bschan9228/MInG/Website/images/FP_slide.png

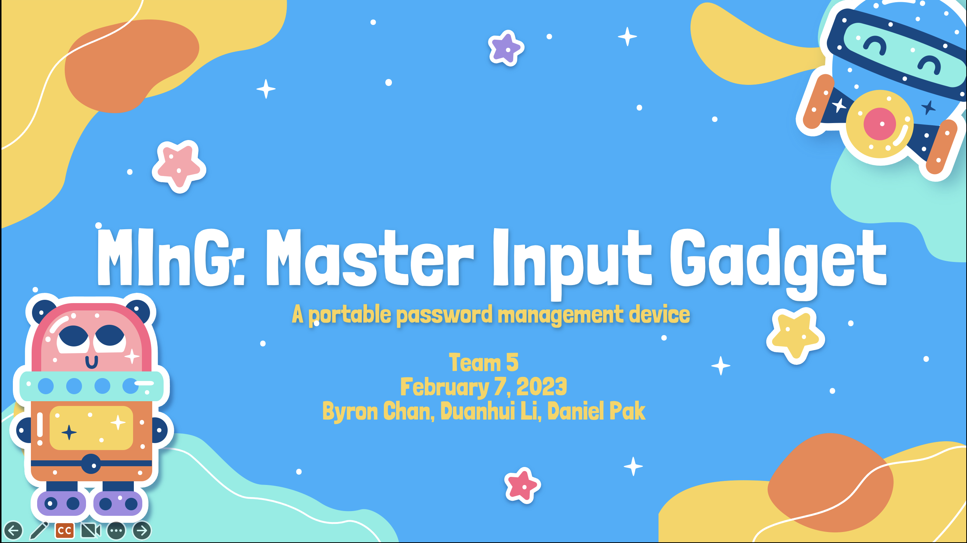
Website/images/FP_slide.png
