bschan9228/MInG/Website/images/IMG_0258.jpg

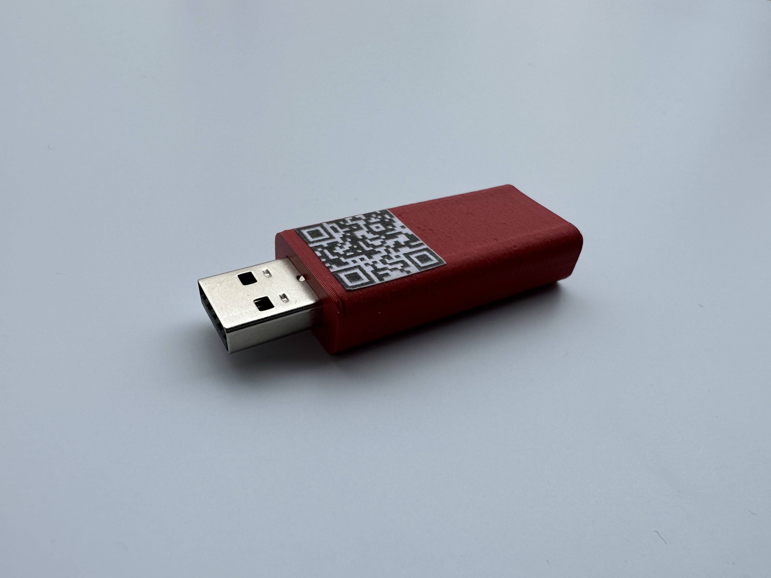
Website/images/IMG_0258.jpg
