bschan9228/MInG/Website/images/IMG_0273.jpg

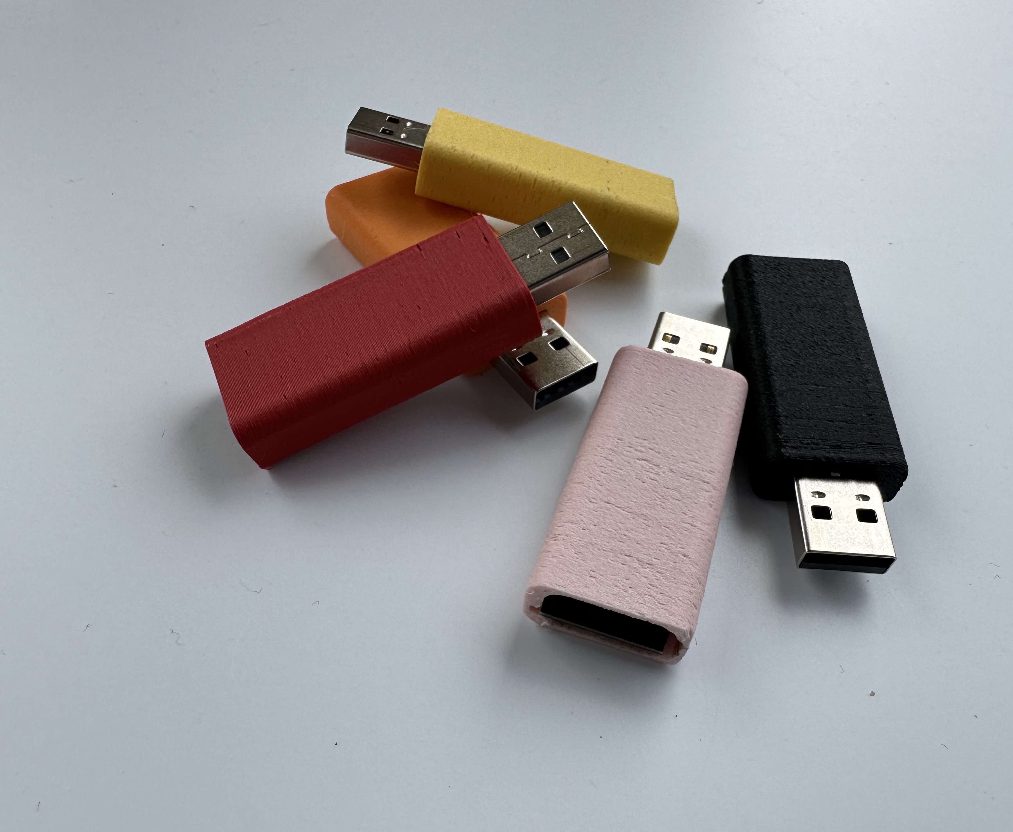
Website/images/IMG_0273.jpg
