bschan9228/MInG/Website/images/IMG_0285.jpg

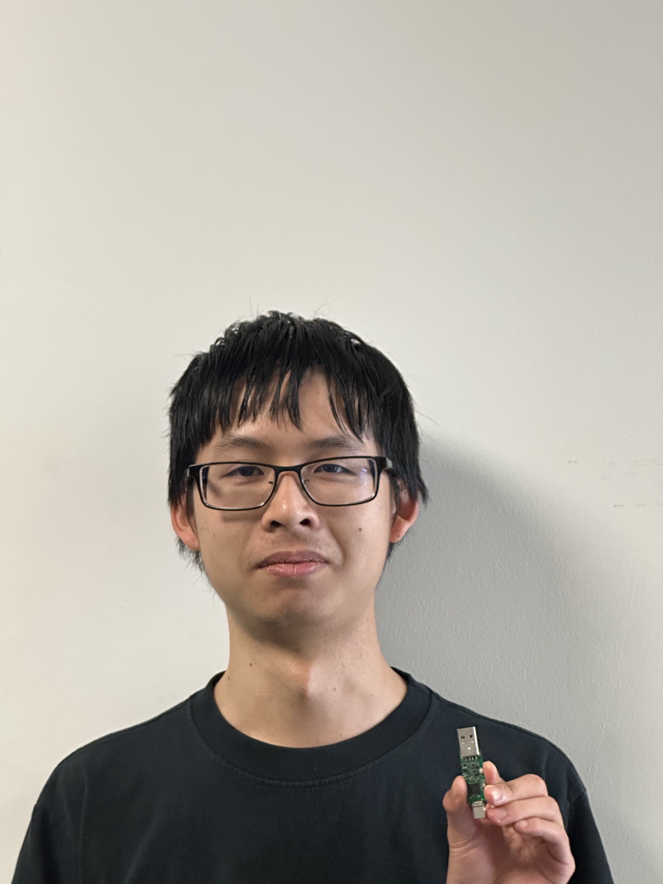
Website/images/IMG_0285.jpg
