bschan9228/MInG/Website/images/IMG_0287.jpg

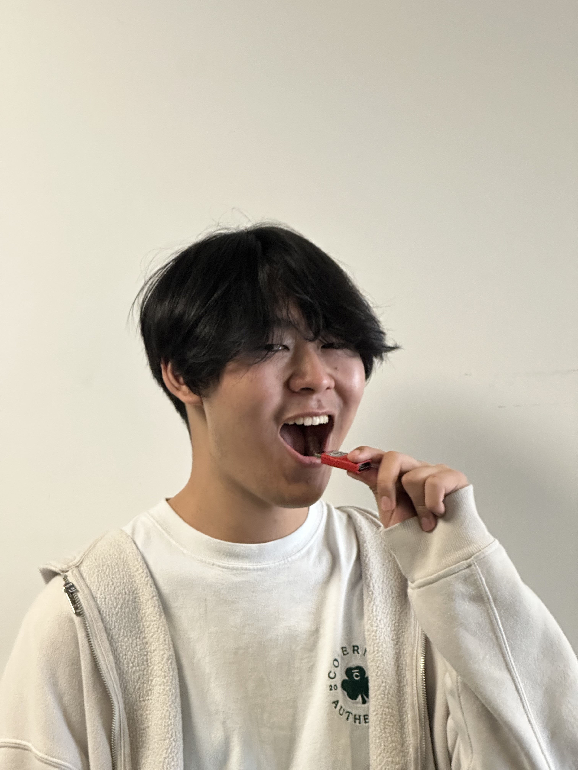
Website/images/IMG_0287.jpg
