bschan9228/MInG/Website/images/IMG_2324.jpg

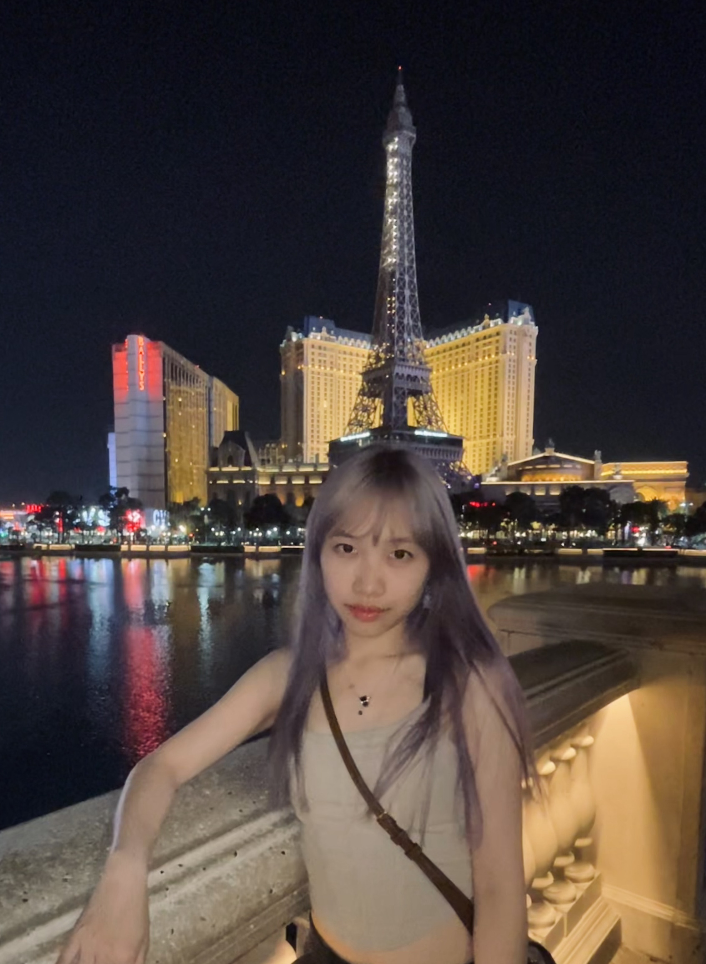
Website/images/IMG_2324.jpg
