bschan9228/MInG/Website/images/mountain.jpeg

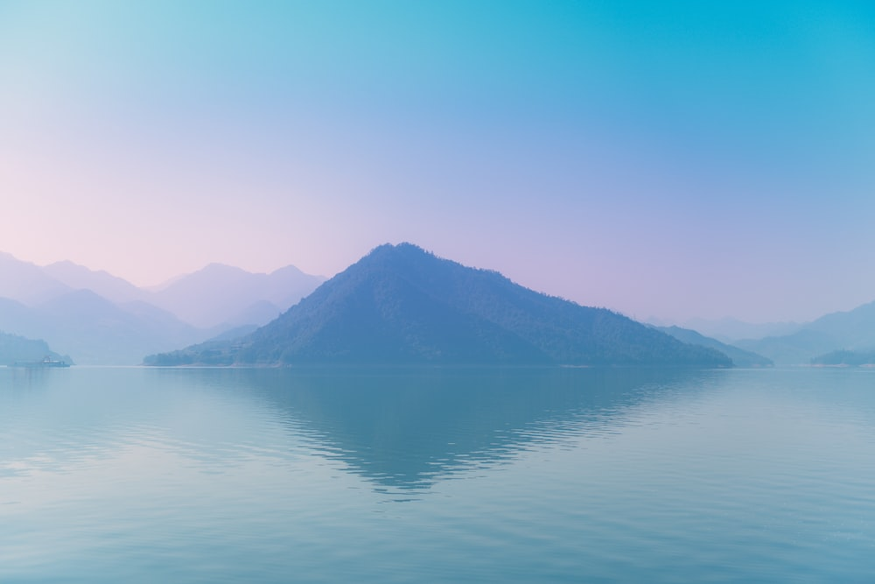
Website/images/mountain.jpeg
