bschan9228/MInG/Website/images/square.jpeg

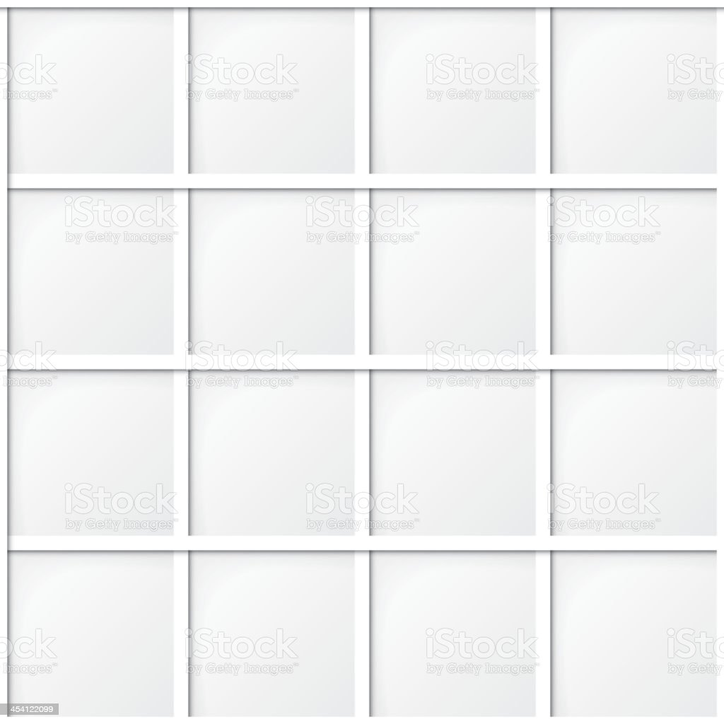
Website/images/square.jpeg
