bschan9228/MInG/Website/images/UCSD-JacobsSchool-USpace_explainer_1@4x_0.png

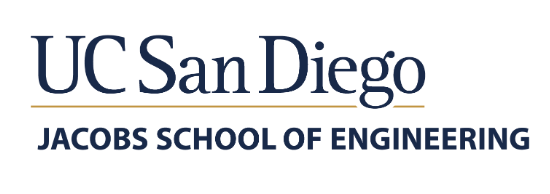
Website/images/UCSD-JacobsSchool-USpace_explainer_1@4x_0.png
