bschan9228/MInG/Website/images/usb1.png

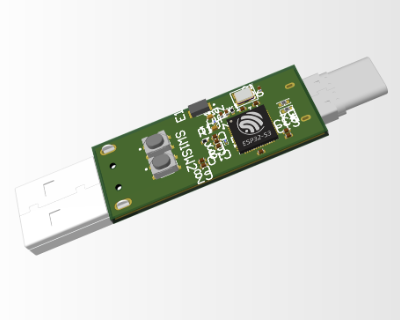
Website/images/usb1.png
