bschan9228/MInG/Website/images/usb2.png

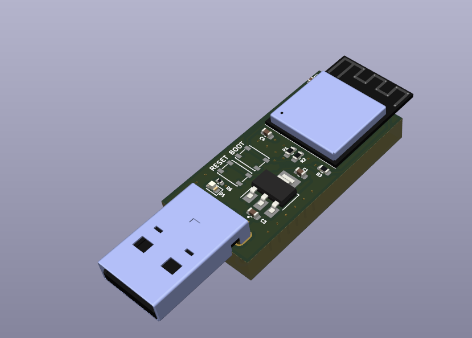
Website/images/usb2.png
