bschan9228/MInG/Website/images/usb33.jpg

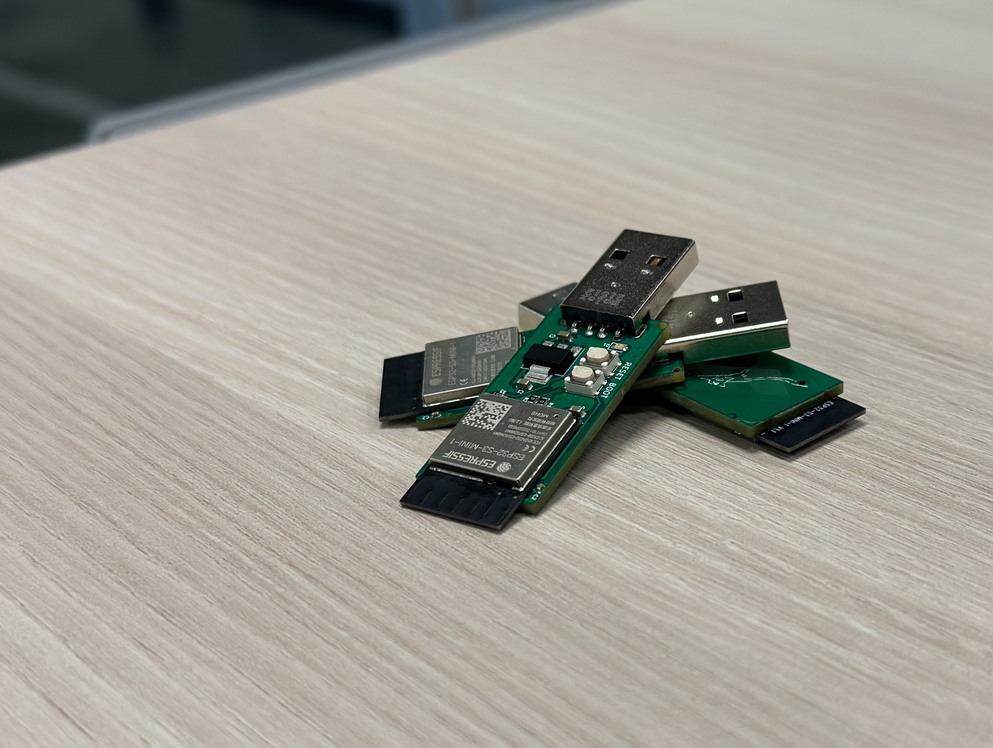
Website/images/usb33.jpg
