bschan9228/MInG/Website/images/vis.png

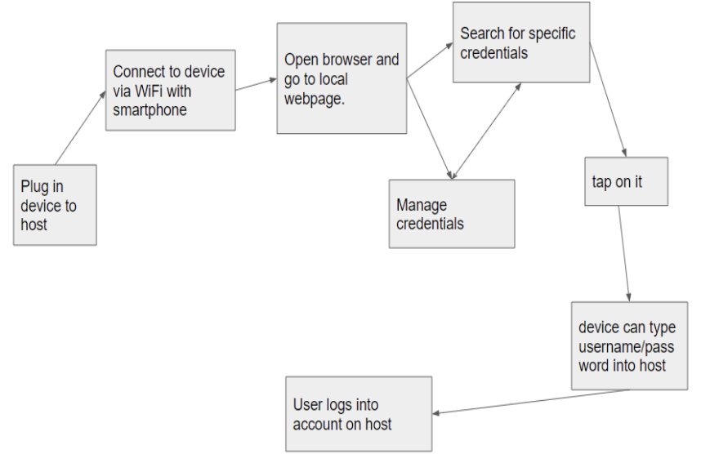
Website/images/vis.png
